Tuetuopay/antboard/hub.sch

## KiCad design hub.sch (2020-03-28)

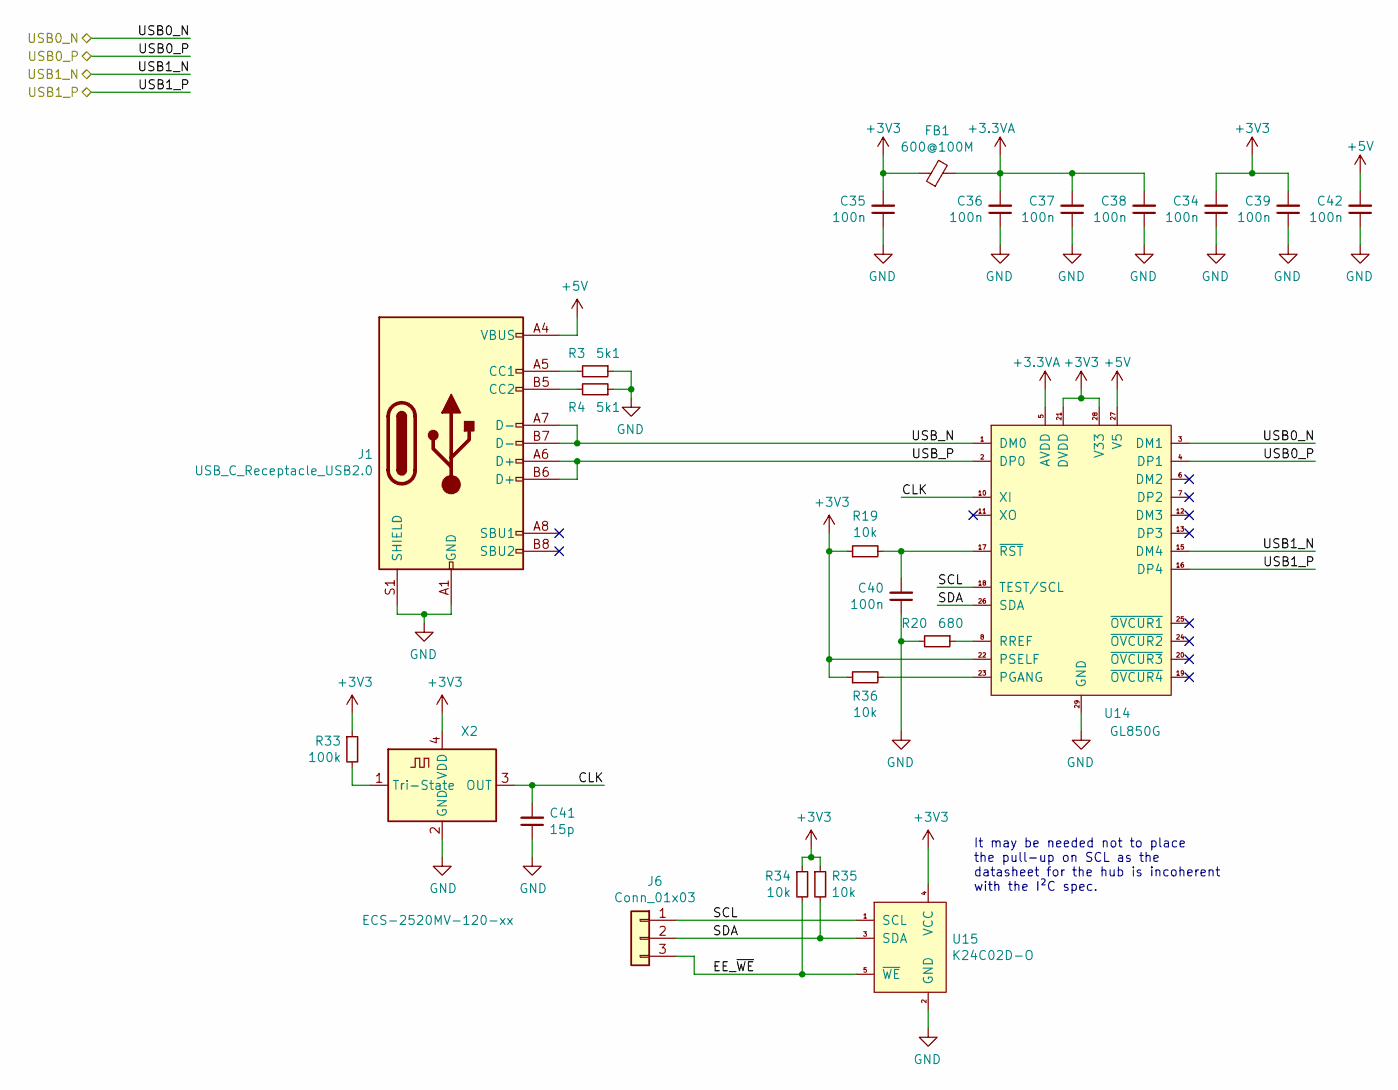
[picture p9: schematic hub.sch]

Parts:
C34, C35, C36, C37, C38, C39, C40, C42: 100n; C_0603_1608Metric; MFR P/N CL10B104KB8NNNC; LCSC P/N C1591
C41: 15p; C_0603_1608Metric; MFR P/N CL10C150JB8NNNC; LCSC P/N C1644
FB1: 600@100M; L_0603_1608Metric; MFR P/N MMZ1608Y601BTA00; LCSC P/N C136491
J1: USB_C_Receptacle_USB2.0; USB_C_Receptacle_Palconn_UTC16-G; MFR P/N TYPE-C-31-M-12; LCSC P/N C165948
J6: Conn_01x03; PinHeader_1x03_P2.54mm_Vertical; MFR P/N C49257; LCSC P/N C49257
R3, R4: 5k1; R_0603_1608Metric; MFR P/N RS-03K5101FT; LCSC P/N C156350
R19, R34, R35, R36: 10k; R_0603_1608Metric; MFR P/N RS-03K1002FT; LCSC P/N C115324
R20: 680; R_0603_1608Metric; MFR P/N RS-03K6800FT; LCSC P/N C88607
R33: 100k; R_0603_1608Metric; MFR P/N MR06X1003FTL; LCSC P/N C327826
U14: GL850G; QFN-28-1EP_5x5mm_P0.5mm_EP3.35x3.35mm_ThermalVias; MFR P/N GL850G-OHY37; LCSC P/N C127278
U15: K24C02D-O; SOT-23-5; MFR P/N K24C02; LCSC P/N C84964
X2: ECS-2520MV-120-xx; Oscillator_SMD_ECS_2520MV-xxx-xx-4Pin_2.5x2.0mm; MFR P/N ECS-2520MV-120-BN-TR; LCSC P/N C405460

Connections:
+3.3VA: C36.2, C37.2, C38.2, FB1.2, U14.5 (AVDD), U14.9 (AVDD), U14.14 (AVDD)
+3V3: C34.2, C35.2, C39.2, FB1.1, R19.1, R33.1, R34.1, R35.1, R36.1, U14.21 (DVDD), U14.22 (PSELF), U14.28 (V33), U15.4 (VCC), X2.4 (VDD)
+5V: C42.2, J1.A4 (VBUS), J1.A9 (VBUS), J1.B4 (VBUS), J1.B9 (VBUS), U14.27 (V5)
CLK: C41.2, U14.10 (XI), X2.3 (OUT)
EE_~WE: J6.3, R34.2, U15.5 (~WE)
GND: C34.1, C35.1, C36.1, C37.1, C38.1, C39.1, C40.1, C41.1, C42.1, J1.A1 (GND), J1.A12 (GND), J1.B1 (GND), J1.B12 (GND), J1.S1 (SHIELD), R3.1, R4.1, R20.2, U14.29 (GND), U15.2 (GND), X2.2 (GND)
unnamed: C40.2, R19.2, U14.17 (~RST)
unnamed: J1.A5 (CC1), R3.2
unnamed: J1.B5 (CC2), R4.2
unnamed: R20.1, U14.8 (RREF)
unnamed: R33.2, X2.1 (Tri-State)
unnamed: R36.2, U14.23 (PGANG)
SCL: J6.1, U14.18 (TEST/SCL), U15.1 (SCL)
SDA: J6.2, R35.2, U14.26 (SDA), U15.3 (SDA)
USB0_N: U14.3 (DM1)
USB0_P: U14.4 (DP1)
USB1_N: U14.15 (DM4)
USB1_P: U14.16 (DP4)
USB_N: J1.A7 (D-), J1.B7 (D-), U14.1 (DM0)
USB_P: J1.A6 (D+), J1.B6 (D+), U14.2 (DP0)

Notes on the sheet:
It may be needed not to place the pull-up on SCL as the datasheet for the hub is incoherent with the I²C spec.
