Tuetuopay/antboard/io.sch

## KiCad design io.sch (2020-03-28)

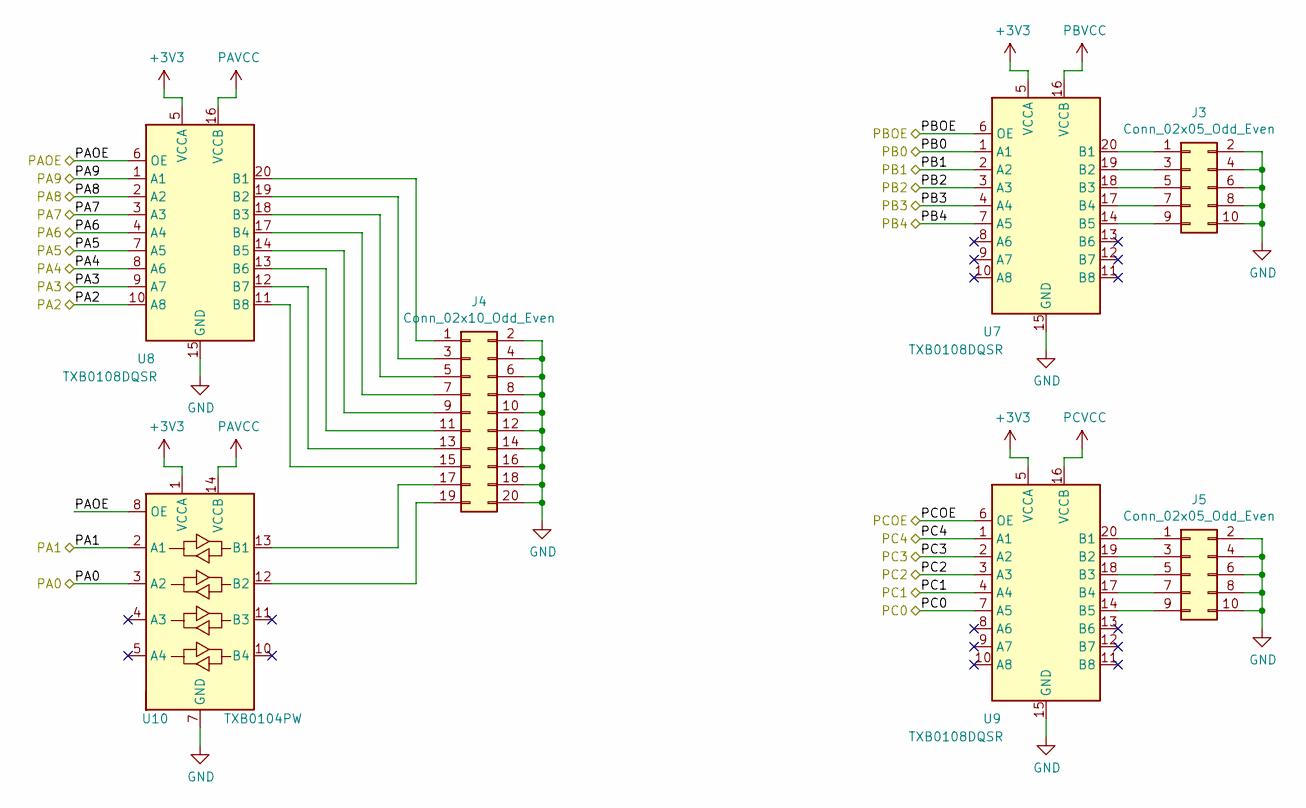
[picture p10: schematic io.sch]

Parts:
J3, J5: Conn_02x05_Odd_Even; PinHeader_2x05_P1.27mm_Vertical_SMD; MFR P/N 20021121-00010C4LF; LCSC P/N C150517
J4: Conn_02x10_Odd_Even; PinHeader_2x10_P1.27mm_Vertical_SMD; MFR P/N C59981; LCSC P/N C59981
U7, U8, U9: TXB0108DQSR; TSSOP-20_4.4x6.5mm_P0.65mm; MFR P/N TXB0108PWR; LCSC P/N C53406
U10: TXB0104PW; TSSOP-14_4.4x5mm_P0.65mm; MFR P/N TXB0104PWR; LCSC P/N C60708

Connections:
+3V3: U7.5 (VCCA), U8.5 (VCCA), U9.5 (VCCA), U10.1 (VCCA)
GND: J3.2, J3.4, J3.6, J3.8, J3.10, J4.2, J4.4, J4.6, J4.8, J4.10, J4.12, J4.14, J4.16, J4.18, J4.20, J5.2, J5.4, J5.6, J5.8, J5.10, U7.15 (GND), U8.15 (GND), U9.15 (GND), U10.7 (GND)
unnamed: J3.1, U7.20 (B1)
unnamed: J3.3, U7.19 (B2)
unnamed: J3.5, U7.18 (B3)
unnamed: J3.7, U7.17 (B4)
unnamed: J3.9, U7.14 (B5)
unnamed: J4.1, U8.20 (B1)
unnamed: J4.3, U8.19 (B2)
unnamed: J4.5, U8.18 (B3)
unnamed: J4.7, U8.17 (B4)
unnamed: J4.9, U8.14 (B5)
unnamed: J4.11, U8.13 (B6)
unnamed: J4.13, U8.12 (B7)
unnamed: J4.15, U8.11 (B8)
unnamed: J4.17, U10.13 (B1)
unnamed: J4.19, U10.12 (B2)
unnamed: J5.1, U9.20 (B1)
unnamed: J5.3, U9.19 (B2)
unnamed: J5.5, U9.18 (B3)
unnamed: J5.7, U9.17 (B4)
unnamed: J5.9, U9.14 (B5)
PA0: U10.3 (A2)
PA1: U10.2 (A1)
PA2: U8.10 (A8)
PA3: U8.9 (A7)
PA4: U8.8 (A6)
PA5: U8.7 (A5)
PA6: U8.4 (A4)
PA7: U8.3 (A3)
PA8: U8.2 (A2)
PA9: U8.1 (A1)
PAOE: U8.6 (OE), U10.8 (OE)
PAVCC: U8.16 (VCCB), U10.14 (VCCB)
PB0: U7.1 (A1)
PB1: U7.2 (A2)
PB2: U7.3 (A3)
PB3: U7.4 (A4)
PB4: U7.7 (A5)
PBOE: U7.6 (OE)
PBVCC: U7.16 (VCCB)
PC0: U9.7 (A5)
PC1: U9.4 (A4)
PC2: U9.3 (A3)
PC3: U9.2 (A2)
PC4: U9.1 (A1)
PCOE: U9.6 (OE)
PCVCC: U9.16 (VCCB)
