Tuetuopay/antboard/io_power.sch

## KiCad design io_power.sch (2020-03-30)

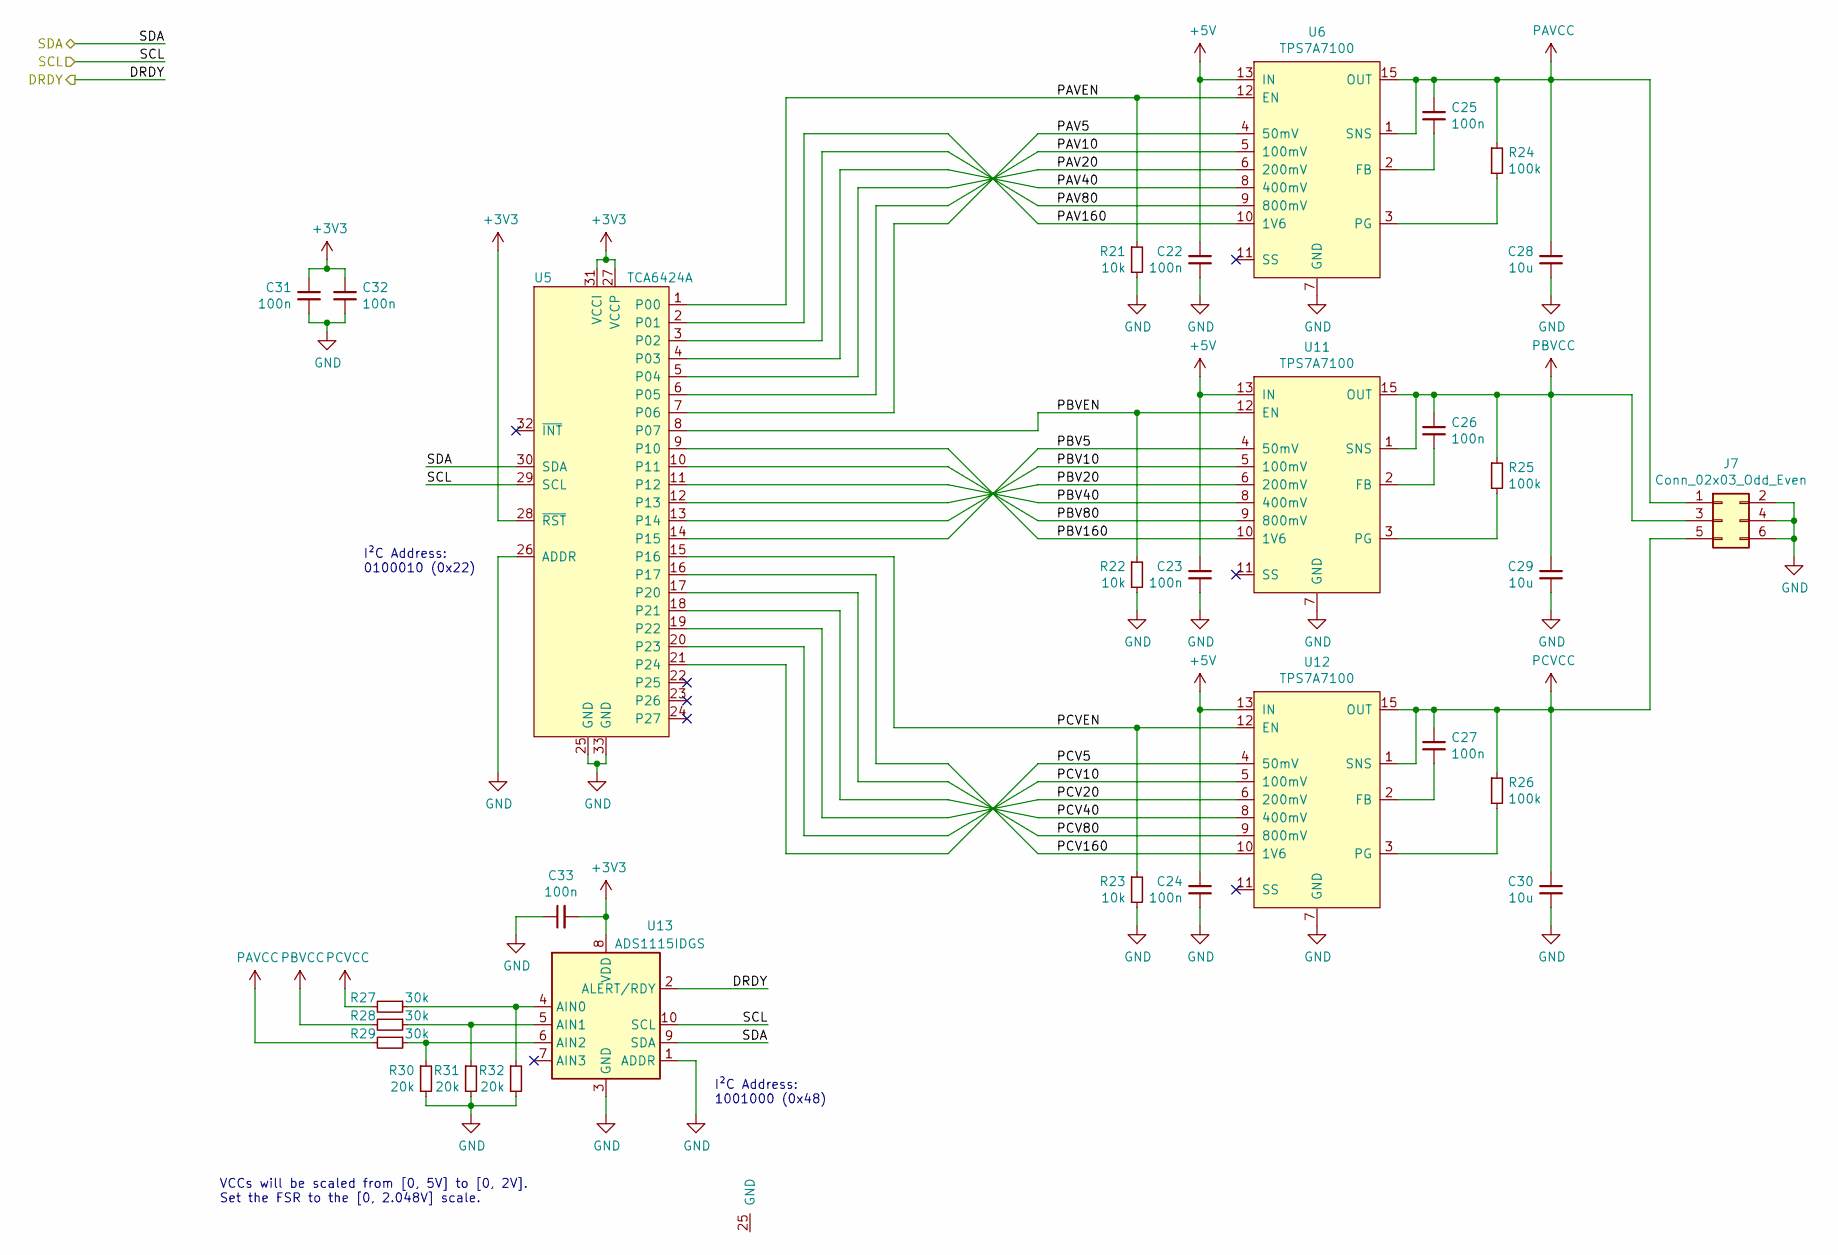
[picture p11: schematic io_power.sch]

Parts:
C22, C23, C24, C25, C26, C27, C31, C32, C33: 100n; C_0603_1608Metric; MFR P/N CL10B104KB8NNNC; LCSC P/N C1591
C28, C29, C30: 10u; C_0603_1608Metric; MFR P/N CL10A106KP8NNNC; LCSC P/N C19702
J7: Conn_02x03_Odd_Even; PinHeader_2x03_P2.54mm_Vertical; MFR P/N C65114; LCSC P/N C65114
R21, R22, R23: 10k; R_0603_1608Metric; MFR P/N RS-03K1002FT; LCSC P/N C115324
R24, R25, R26: 100k; R_0603_1608Metric; MFR P/N MR06X1003FTL; LCSC P/N C327826
R27, R28, R29: 30k; R_0603_1608Metric; MFR P/N ERJPB3B3002V; LCSC P/N C413703
R30, R31, R32: 20k; R_0603_1608Metric; MFR P/N ERJPB3B2002V; LCSC P/N C191225
U5: TCA6424A; QFN-32-1EP_5x5mm_P0.5mm_EP3.1x3.1mm; MFR P/N TCA6424ARGJR; LCSC P/N C80692
U6, U11, U12: TPS7A7100; VQFN-16-1EP_3x3mm_P0.5mm_EP1.6x1.6mm_ThermalVias; MFR P/N TPS7A7100RGTR; LCSC P/N C129327
U13: ADS1115IDGS; TSSOP-10_3x3mm_P0.5mm; MFR P/N ADS1115IDGSR; LCSC P/N C37593

Connections:
+3V3: C31.1, C32.1, C33.2, U5.27 (VCCP), U5.28 (~RST), U5.31 (VCCI), U13.8 (VDD)
+5V: C22.1, C23.1, C24.1, U6.13 (IN), U6.14 (IN), U11.13 (IN), U11.14 (IN), U12.13 (IN), U12.14 (IN)
DRDY: U13.2 (ALERT/RDY)
GND: C22.2, C23.2, C24.2, C28.2, C29.2, C30.2, C31.2, C32.2, C33.1, J7.2, J7.4, J7.6, R21.2, R22.2, R23.2, R30.2, R31.2, R32.2, U5.25 (GND), U5.26 (ADDR), U5.33 (GND), U6.7 (GND), U11.7 (GND), U12.7 (GND), U13.1 (ADDR), U13.3 (GND)
unnamed: C25.2, U6.2 (FB)
unnamed: C26.2, U11.2 (FB)
unnamed: C27.2, U12.2 (FB)
unnamed: R24.2, U6.3 (PG)
unnamed: R25.2, U11.3 (PG)
unnamed: R26.2, U12.3 (PG)
unnamed: R27.1, R32.1, U13.4 (AIN0)
unnamed: R28.1, R31.1, U13.5 (AIN1)
unnamed: R29.1, R30.1, U13.6 (AIN2)
PAV5: U5.7 (P06), U6.4 (50mV)
PAV10: U5.6 (P05), U6.5 (100mV)
PAV20: U5.5 (P04), U6.6 (200mV)
PAV40: U5.4 (P03), U6.8 (400mV)
PAV80: U5.3 (P02), U6.9 (800mV)
PAV160: U5.2 (P01), U6.10 (1V6)
PAVCC: C25.1, C28.1, J7.1, R24.1, R29.2, U6.1 (SNS), U6.15 (OUT), U6.16 (OUT)
PAVEN: R21.1, U5.1 (P00), U6.12 (EN)
PBV5: U5.14 (P15), U11.4 (50mV)
PBV10: U5.13 (P14), U11.5 (100mV)
PBV20: U5.12 (P13), U11.6 (200mV)
PBV40: U5.11 (P12), U11.8 (400mV)
PBV80: U5.10 (P11), U11.9 (800mV)
PBV160: U5.9 (P10), U11.10 (1V6)
PBVCC: C26.1, C29.1, J7.3, R25.1, R28.2, U11.1 (SNS), U11.15 (OUT), U11.16 (OUT)
PBVEN: R22.1, U5.8 (P07), U11.12 (EN)
PCV5: U5.21 (P24), U12.4 (50mV)
PCV10: U5.20 (P23), U12.5 (100mV)
PCV20: U5.19 (P22), U12.6 (200mV)
PCV40: U5.18 (P21), U12.8 (400mV)
PCV80: U5.17 (P20), U12.9 (800mV)
PCV160: U5.16 (P17), U12.10 (1V6)
PCVCC: C27.1, C30.1, J7.5, R26.1, R27.2, U12.1 (SNS), U12.15 (OUT), U12.16 (OUT)
PCVEN: R23.1, U5.15 (P16), U12.12 (EN)
SCL: U5.29 (SCL), U13.10 (SCL)
SDA: U5.30 (SDA), U13.9 (SDA)

Notes on the sheet:
I²C Address: 0100010 (0x22)
I²C Address: 1001000 (0x48)
VCCs will be scaled from [0, 5V] to [0, 2V]. Set the FSR to the [0, 2.048V] scale.
