Tuetuopay/antboard/st_link.sch

## KiCad design st_link.sch (2020-03-31, an earlier design)

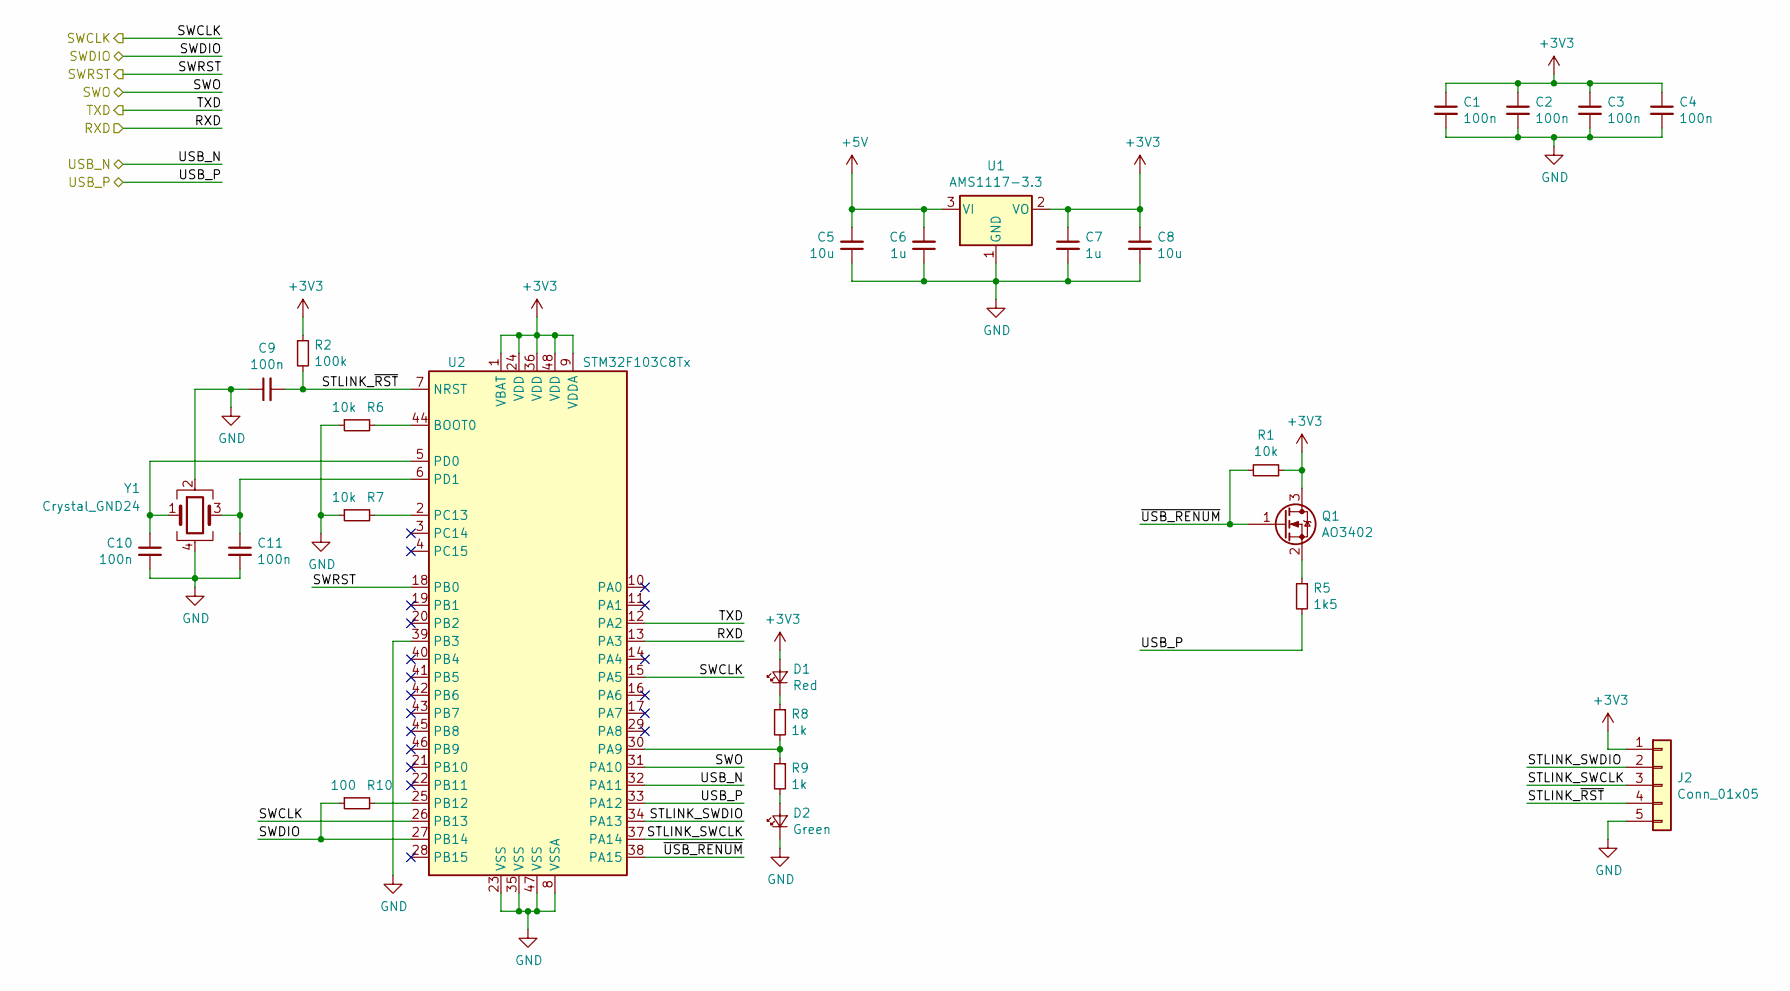
[picture p12: schematic st_link.sch]

Parts:
C1, C2, C3, C4, C9, C10, C11: 100n; C_0603_1608Metric; MFR P/N CL10B104KB8NNNC; LCSC P/N C1591
C5, C8: 10u; C_0603_1608Metric; MFR P/N CL10A106KP8NNNC; LCSC P/N C19702
C6, C7: 1u; C_0603_1608Metric; MFR P/N CL10B105KP8NNNC; LCSC P/N C95843
D1: Red; LED_0603_1608Metric; MFR P/N LTST-C193KRKT-5A; LCSC P/N C157741
D2: Green; LED_0603_1608Metric; MFR P/N LTST-C193KGKT-5A; LCSC P/N C125102
J2: Conn_01x05; PinHeader_1x05_P2.54mm_Vertical; MFR P/N C138801; LCSC P/N C138801
Q1: AO3402; SOT-23; MFR P/N AO3402; LCSC P/N C427384
R1, R6, R7: 10k; R_0603_1608Metric; MFR P/N RS-03K1002FT; LCSC P/N C115324
R2: 100k; R_0603_1608Metric; MFR P/N MR06X1003FTL; LCSC P/N C327826
R5: 1k5; R_0603_1608Metric; MFR P/N RS-03K1501FT; LCSC P/N C118397
R8, R9: 1k; R_0603_1608Metric; MFR P/N SY0603JN1KP; LCSC P/N C380759
R10: 100; R_0603_1608Metric; MFR P/N RS-03K1000FT; LCSC P/N C115420
U1: AMS1117-3.3; SOT-223-3_TabPin2; MFR P/N AMS1117-3.3; LCSC P/N C426566
U2: STM32F103C8Tx; LQFP-48_7x7mm_P0.5mm; MFR P/N STM32F103C8T6; LCSC P/N C8734
Y1: Crystal_GND24; Crystal_SMD_3225-4Pin_3.2x2.5mm; MFR P/N TAXM8M4RDBCCT2T; LCSC P/N C400090

Connections:
+3V3: C1.1, C2.1, C3.1, C4.1, C7.1, C8.1, D1.2 (A), J2.1, Q1.3 (D), R1.1, R2.1, U1.2 (VO), U2.1 (VBAT), U2.9 (VDDA), U2.24 (VDD), U2.36 (VDD), U2.48 (VDD)
+5V: C5.2, C6.2, U1.3 (VI)
GND: C1.2, C2.2, C3.2, C4.2, C5.1, C6.1, C7.2, C8.2, C9.1, C10.2, C11.2, D2.1 (K), J2.5, R6.1, R7.1, U1.1 (GND), U2.8 (VSSA), U2.23 (VSS), U2.35 (VSS), U2.39 (PB3), U2.47 (VSS), Y1.2, Y1.4
unnamed: C10.1, U2.5 (PD0), Y1.1
unnamed: C11.1, U2.6 (PD1), Y1.3
unnamed: D1.1 (K), R8.1
unnamed: D2.2 (A), R9.2
unnamed: Q1.2 (S), R5.1
unnamed: R6.2, U2.44 (BOOT0)
unnamed: R7.2, U2.2 (PC13)
unnamed: R8.2, R9.1, U2.30 (PA9)
unnamed: R10.2, U2.25 (PB12)
RXD: U2.13 (PA3)
STLINK_SWCLK: J2.3, U2.37 (PA14)
STLINK_SWDIO: J2.2, U2.34 (PA13)
STLINK_~RST: C9.2, J2.4, R2.2, U2.7 (NRST)
SWCLK: U2.15 (PA5), U2.26 (PB13)
SWDIO: R10.1, U2.27 (PB14)
SWO: U2.31 (PA10)
SWRST: U2.18 (PB0)
TXD: U2.12 (PA2)
USB_N: U2.32 (PA11)
USB_P: R5.2, U2.33 (PA12)
~USB_RENUM: Q1.1 (G), R1.2, U2.38 (PA15)
