Tuetuopay/antboard/stm32.sch

## KiCad design stm32.sch (2020-03-31, an earlier design)

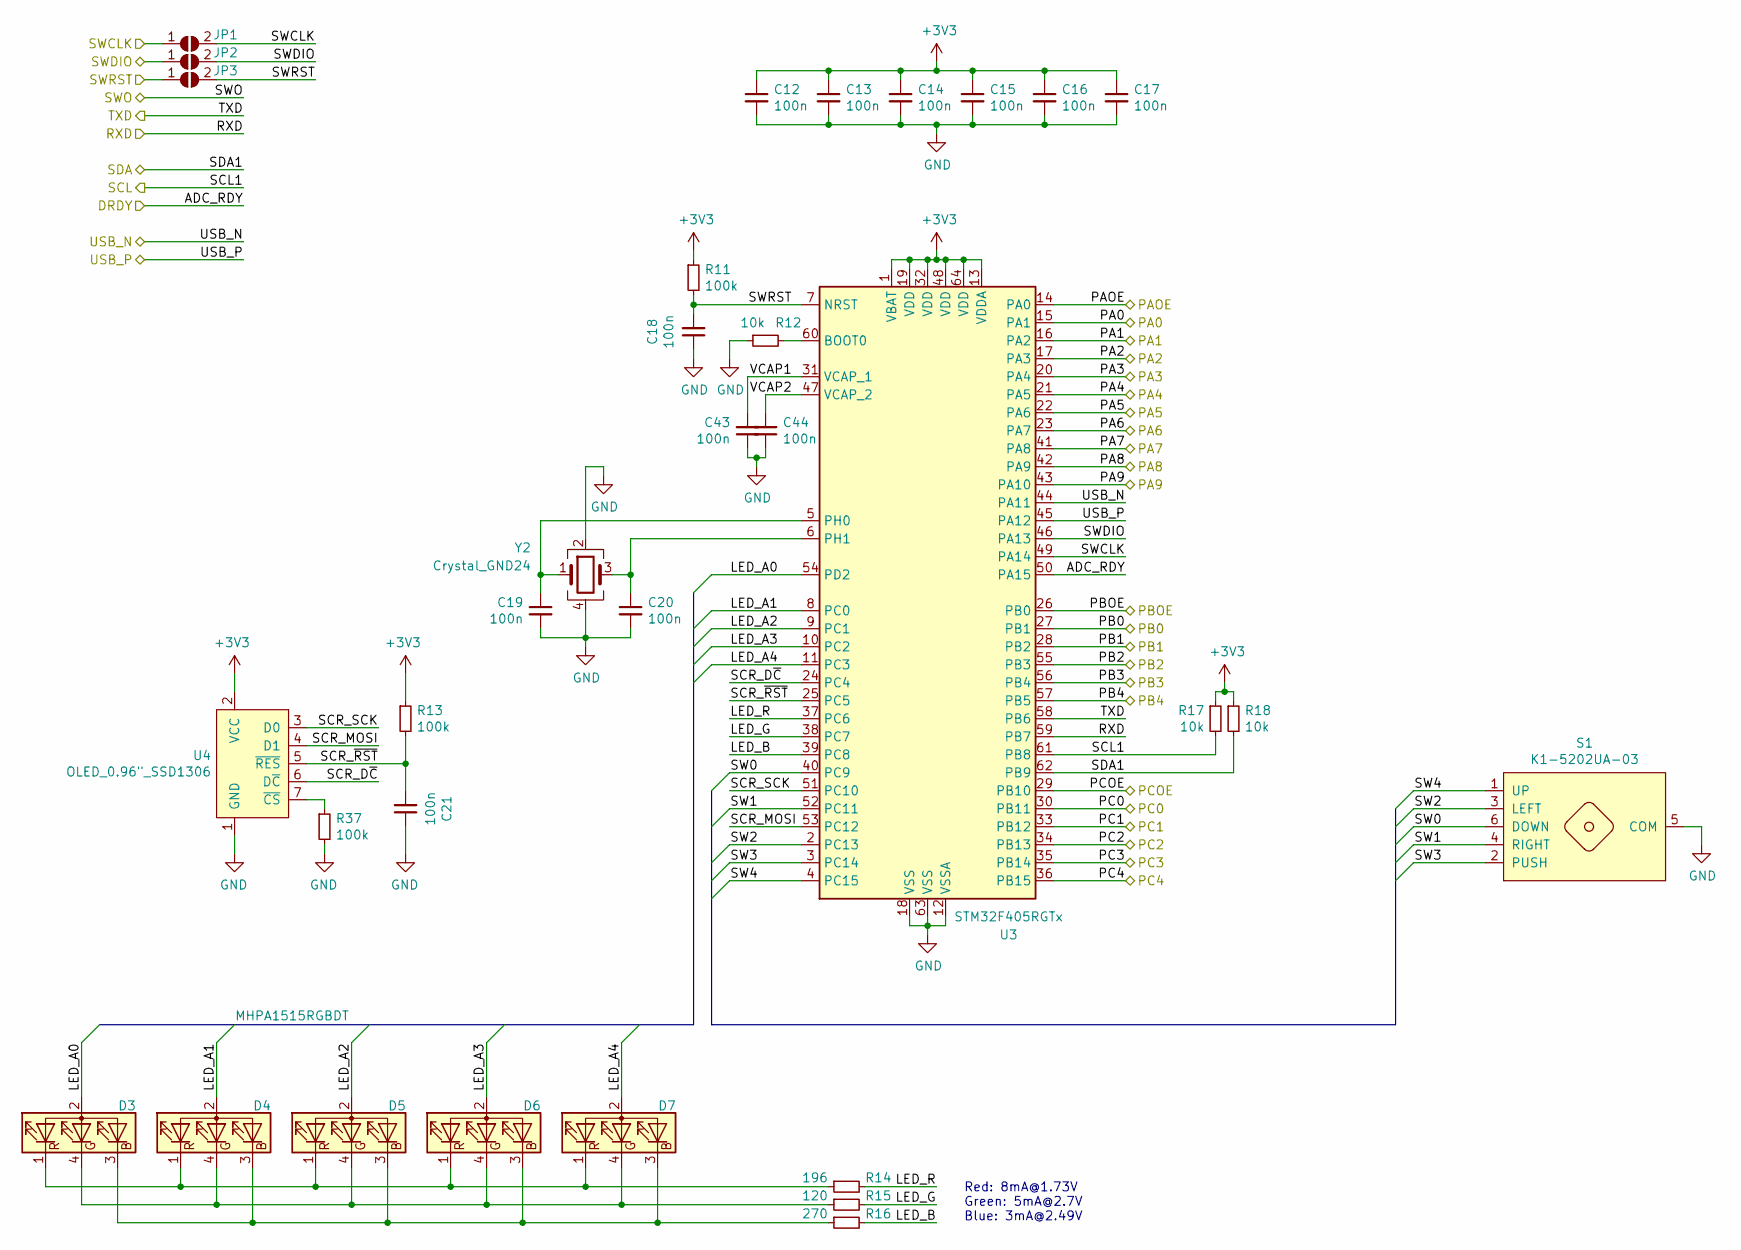
[picture p13: schematic stm32.sch]

Parts:
C12, C13, C14, C15, C16, C17, C18, C19, C20, C21, C43, C44: 100n; C_0603_1608Metric; MFR P/N CL10B104KB8NNNC; LCSC P/N C1591
D3, D4, D5, D6, D7: MHPA1515RGBDT; PLCC1515; MFR P/N MHPA1515RGBDT; LCSC P/N C404281
JP1, JP2, JP3: SolderJumper_2_Bridged; R_0603_1608Metric
R11, R13, R37: 100k; R_0603_1608Metric; MFR P/N MR06X1003FTL; LCSC P/N C327826
R12, R17, R18: 10k; R_0603_1608Metric; MFR P/N RS-03K1002FT; LCSC P/N C115324
R14: 196; R_0603_1608Metric; MFR P/N CR0603F196RP05; LCSC P/N C429538
R15: 120; R_0603_1608Metric; MFR P/N 0603WAF1200T5E; LCSC P/N C22787
R16: 270; R_0603_1608Metric; MFR P/N RS-03K2700FT; LCSC P/N C286581
S1: K1-5202UA-03; MFR P/N K1-5202UA-03; LCSC P/N C145899
U3: STM32F405RGTx; LQFP-64_10x10mm_P0.5mm; MFR P/N STM32F405RGT6; LCSC P/N C15742
U4: OLED_0.96\"_SSD1306; OLED_0.96_SSD1306; MFR P/N MTF185-107SY1; LCSC P/N C358721
Y2: Crystal_GND24; Crystal_SMD_3225-4Pin_3.2x2.5mm; MFR P/N TAXM8M4RDBCCT2T; LCSC P/N C400090

Connections:
+3V3: C12.1, C13.1, C14.1, C15.1, C16.1, C17.1, R11.1, R13.1, R17.1, R18.1, U3.1 (VBAT), U3.13 (VDDA), U3.19 (VDD), U3.32 (VDD), U3.48 (VDD), U3.64 (VDD), U4.2 (VCC)
ADC_RDY: U3.50 (PA15)
GND: C12.2, C13.2, C14.2, C15.2, C16.2, C17.2, C18.1, C19.2, C20.2, C21.1, C43.1, C44.1, R12.1, R37.2, S1.5 (COM), U3.12 (VSSA), U3.18 (VSS), U3.63 (VSS), U4.1 (GND), Y2.2, Y2.4
LED_A0: D3.2 (A), U3.54 (PD2)
LED_A1: D4.2 (A), U3.8 (PC0)
LED_A2: D5.2 (A), U3.9 (PC1)
LED_A3: D6.2 (A), U3.10 (PC2)
LED_A4: D7.2 (A), U3.11 (PC3)
LED_B: R16.2, U3.39 (PC8)
LED_G: R15.2, U3.38 (PC7)
LED_R: R14.2, U3.37 (PC6)
unnamed: C19.1, U3.5 (PH0), Y2.1
unnamed: C20.1, U3.6 (PH1), Y2.3
unnamed: D3.1 (RK), D4.1 (RK), D5.1 (RK), D6.1 (RK), D7.1 (RK), R14.1
unnamed: D3.3 (BK), D4.3 (BK), D5.3 (BK), D6.3 (BK), D7.3 (BK), R16.1
unnamed: D3.4 (GK), D4.4 (GK), D5.4 (GK), D6.4 (GK), D7.4 (GK), R15.1
unnamed: R12.2, U3.60 (BOOT0)
unnamed: R37.1, U4.7 (~CS)
PA0: U3.15 (PA1)
PA1: U3.16 (PA2)
PA2: U3.17 (PA3)
PA3: U3.20 (PA4)
PA4: U3.21 (PA5)
PA5: U3.22 (PA6)
PA6: U3.23 (PA7)
PA7: U3.41 (PA8)
PA8: U3.42 (PA9)
PA9: U3.43 (PA10)
PAOE: U3.14 (PA0)
PB0: U3.27 (PB1)
PB1: U3.28 (PB2)
PB2: U3.55 (PB3)
PB3: U3.56 (PB4)
PB4: U3.57 (PB5)
PBOE: U3.26 (PB0)
PC0: U3.30 (PB11)
PC1: U3.33 (PB12)
PC2: U3.34 (PB13)
PC3: U3.35 (PB14)
PC4: U3.36 (PB15)
PCOE: U3.29 (PB10)
RXD: U3.59 (PB7)
SCL: R17.2, U3.61 (PB8)
SCR_D~C: U3.24 (PC4), U4.6 (D~C)
SCR_MOSI: U3.53 (PC12), U4.4 (D1)
SCR_SCK: U3.51 (PC10), U4.3 (D0)
SCR_~RST: C21.2, R13.2, U3.25 (PC5), U4.5 (~RES)
SDA: R18.2, U3.62 (PB9)
SW0: S1.6 (DOWN), U3.40 (PC9)
SW1: S1.4 (RIGHT), U3.52 (PC11)
SW2: S1.3 (LEFT), U3.2 (PC13)
SW3: S1.2 (PUSH), U3.3 (PC14)
SW4: S1.1 (UP), U3.4 (PC15)
SWCLK: JP1.1 (A), JP1.2 (B), U3.49 (PA14)
SWDIO: JP2.1 (A), JP2.2 (B), U3.46 (PA13)
SWRST: C18.2, JP3.1 (A), JP3.2 (B), R11.2, U3.7 (NRST)
TXD: U3.58 (PB6)
USB_N: U3.44 (PA11)
USB_P: U3.45 (PA12)
VCAP1: C43.2, U3.31 (VCAP_1)
VCAP2: C44.2, U3.47 (VCAP_2)

Notes on the sheet:
Red: 8mA@1.73V Green: 5mA@2.7V Blue: 3mA@2.49V
